DarmorGamz/Ultrasonic-Flow-Reader/docs/Flowcharts/BlockDiagram.pdf

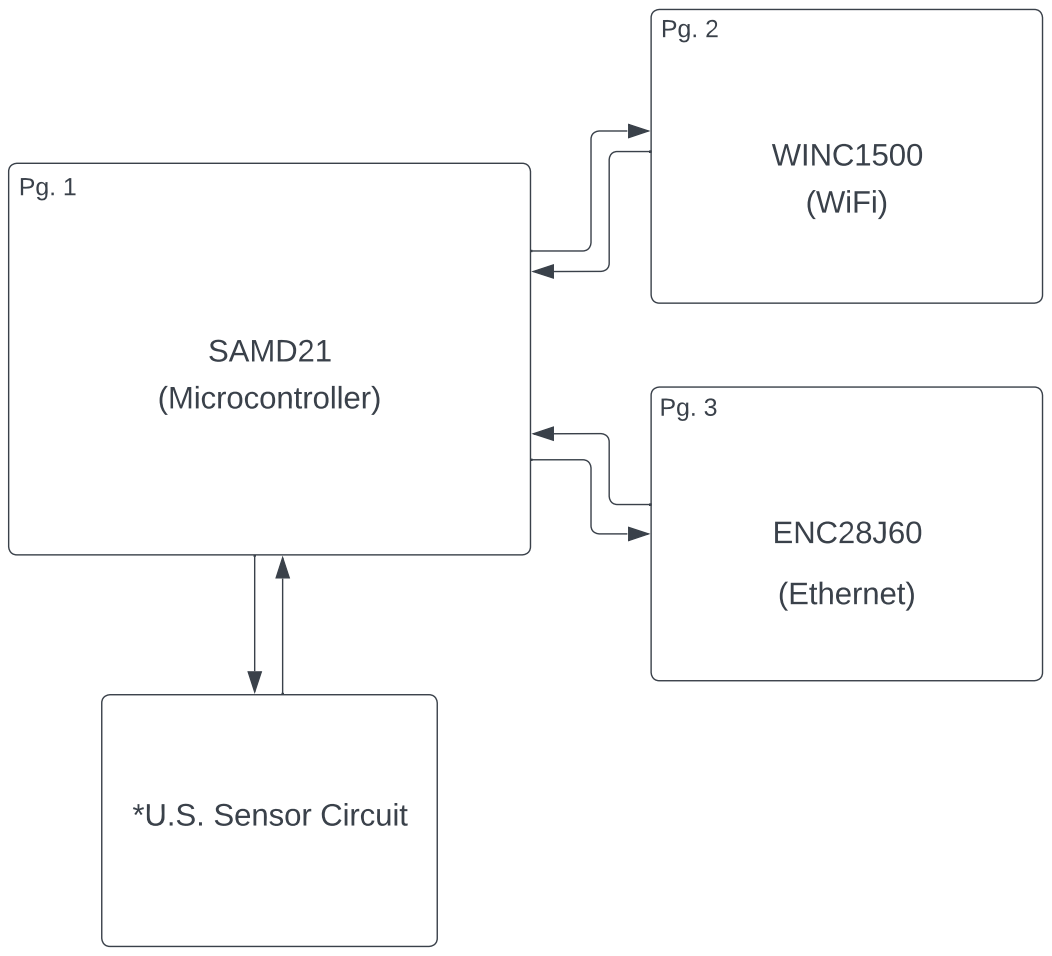
[picture p48: page 1]
SAMD21; WINC1500; ENC28J60; *U.S. Sensor Circuit; (WiFi); (Ethernet); (Microcontroller); DCA

TITLE: Ultrasonic Meter-Reader Block Diagram
REV: v1.0
DATE: 2022/11/02
