DarmorGamz/Ultrasonic-Flow-Reader/Firmware/Firmware/driver_init.h

/*
 * Code generated from Atmel Start.
 *
 * This file will be overwritten when reconfiguring your Atmel Start project.
 * Please copy examples or other code you want to keep to a separate file
 * to avoid losing it when reconfiguring.
 */
#ifndef DRIVER_INIT_INCLUDED
#define DRIVER_INIT_INCLUDED

#include "atmel_start_pins.h"

#ifdef __cplusplus
extern "C" {
#endif

#include <hal_atomic.h>
#include <hal_delay.h>
#include <hal_gpio.h>
#include <hal_init.h>
#include <hal_io.h>
#include <hal_sleep.h>

#include <hal_ext_irq.h>

#include <hal_flash.h>

#include <hal_spi_m_sync.h>
#include <hal_spi_m_sync.h>

#include <hal_delay.h>
#include <hal_timer.h>
#include <hpl_tc_base.h>
#include <hal_timer.h>
#include <hpl_tc_base.h>
#include <hal_timer.h>
#include <hpl_tc_base.h>

#include <hal_wdt.h>

extern struct flash_descriptor      FLASH_0;
extern struct spi_m_sync_descriptor WIRELESS_SPI;
extern struct spi_m_sync_descriptor ETHERNET_SPI;

extern struct timer_descriptor TIMER_0;
extern struct timer_descriptor SAMPLE_TIMER;
extern struct timer_descriptor TICK_TIMER;

extern struct wdt_descriptor WDT_0;

void FLASH_0_init(void);
void FLASH_0_CLOCK_init(void);

void WIRELESS_SPI_PORT_init(void);
void WIRELESS_SPI_CLOCK_init(void);
void WIRELESS_SPI_init(void);

void ETHERNET_SPI_PORT_init(void);
void ETHERNET_SPI_CLOCK_init(void);
void ETHERNET_SPI_init(void);

void delay_driver_init(void);

void WDT_0_CLOCK_init(void);
void WDT_0_init(void);

/**
 * \brief Perform system initialization, initialize pins and clocks for
 * peripherals
 */
void system_init(void);

#ifdef __cplusplus
}
#endif
#endif // DRIVER_INIT_INCLUDED
