DarmorGamz/Ultrasonic-Flow-Reader/Firmware/Firmware/hri/hri_port_d20.h

/**
 * \file
 *
 * \brief SAM PORT
 *
 * Copyright (c) 2017-2018 Microchip Technology Inc. and its subsidiaries.
 *
 * \asf_license_start
 *
 * \page License
 *
 * Subject to your compliance with these terms, you may use Microchip
 * software and any derivatives exclusively with Microchip products.
 * It is your responsibility to comply with third party license terms applicable
 * to your use of third party software (including open source software) that
 * may accompany Microchip software.
 *
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
 * \asf_license_stop
 *
 */

#ifdef _SAMD20_PORT_COMPONENT_
#ifndef _HRI_PORT_D20_H_INCLUDED_
#define _HRI_PORT_D20_H_INCLUDED_

#ifdef __cplusplus
extern "C" {
#endif

#include <stdbool.h>
#include <hal_atomic.h>

#if defined(ENABLE_PORT_CRITICAL_SECTIONS)
#define PORT_CRITICAL_SECTION_ENTER() CRITICAL_SECTION_ENTER()
#define PORT_CRITICAL_SECTION_LEAVE() CRITICAL_SECTION_LEAVE()
#else
#define PORT_CRITICAL_SECTION_ENTER()
#define PORT_CRITICAL_SECTION_LEAVE()
#endif

typedef uint32_t hri_port_ctrl_reg_t;
typedef uint32_t hri_port_dir_reg_t;
typedef uint32_t hri_port_in_reg_t;
typedef uint32_t hri_port_out_reg_t;
typedef uint32_t hri_port_wrconfig_reg_t;
typedef uint32_t hri_portgroup_ctrl_reg_t;
typedef uint32_t hri_portgroup_dir_reg_t;
typedef uint32_t hri_portgroup_in_reg_t;
typedef uint32_t hri_portgroup_out_reg_t;
typedef uint32_t hri_portgroup_wrconfig_reg_t;
typedef uint8_t  hri_port_pincfg_reg_t;
typedef uint8_t  hri_port_pmux_reg_t;
typedef uint8_t  hri_portgroup_pincfg_reg_t;
typedef uint8_t  hri_portgroup_pmux_reg_t;

static inline void hri_portgroup_set_DIR_DIR_bf(const void *const hw, hri_port_dir_reg_t mask)
{
	((PortGroup *)hw)->DIRSET.reg = PORT_DIR_DIR(mask);
}

static inline hri_port_dir_reg_t hri_portgroup_get_DIR_DIR_bf(const void *const hw, hri_port_dir_reg_t mask)
{
	uint32_t tmp;
	tmp = ((PortGroup *)hw)->DIR.reg;
	tmp = (tmp & PORT_DIR_DIR(mask)) >> PORT_DIR_DIR_Pos;
	return tmp;
}

static inline hri_port_dir_reg_t hri_portgroup_read_DIR_DIR_bf(const void *const hw)
{
	uint32_t tmp;
	tmp = ((PortGroup *)hw)->DIR.reg;
	tmp = (tmp & PORT_DIR_DIR_Msk) >> PORT_DIR_DIR_Pos;
	return tmp;
}

static inline void hri_portgroup_write_DIR_DIR_bf(const void *const hw, hri_port_dir_reg_t data)
{
	((PortGroup *)hw)->DIRSET.reg = PORT_DIR_DIR(data);
	((PortGroup *)hw)->DIRCLR.reg = ~PORT_DIR_DIR(data);
}

static inline void hri_portgroup_clear_DIR_DIR_bf(const void *const hw, hri_port_dir_reg_t mask)
{
	((PortGroup *)hw)->DIRCLR.reg = PORT_DIR_DIR(mask);
}

static inline void hri_portgroup_toggle_DIR_DIR_bf(const void *const hw, hri_port_dir_reg_t mask)
{
	((PortGroup *)hw)->DIRTGL.reg = PORT_DIR_DIR(mask);
}

static inline void hri_portgroup_set_DIR_reg(const void *const hw, hri_port_dir_reg_t mask)
{
	((PortGroup *)hw)->DIRSET.reg = mask;
}

static inline hri_port_dir_reg_t hri_portgroup_get_DIR_reg(const void *const hw, hri_port_dir_reg_t mask)
{
	uint32_t tmp;
	tmp = ((PortGroup *)hw)->DIR.reg;
	tmp &= mask;
	return tmp;
}

static inline hri_port_dir_reg_t hri_portgroup_read_DIR_reg(const void *const hw)
{
	return ((PortGroup *)hw)->DIR.reg;
}

static inline void hri_portgroup_write_DIR_reg(const void *const hw, hri_port_dir_reg_t data)
{
	((PortGroup *)hw)->DIRSET.reg = data;
	((PortGroup *)hw)->DIRCLR.reg = ~data;
}

static inline void hri_portgroup_clear_DIR_reg(const void *const hw, hri_port_dir_reg_t mask)
{
	((PortGroup *)hw)->DIRCLR.reg = mask;
}

static inline void hri_portgroup_toggle_DIR_reg(const void *const hw, hri_port_dir_reg_t mask)
{
	((PortGroup *)hw)->DIRTGL.reg = mask;
}

static inline void hri_portgroup_set_OUT_OUT_bf(const void *const hw, hri_port_out_reg_t mask)
{
	((PortGroup *)hw)->OUTSET.reg = PORT_OUT_OUT(mask);
}

static inline hri_port_out_reg_t hri_portgroup_get_OUT_OUT_bf(const void *const hw, hri_port_out_reg_t mask)
{
	uint32_t tmp;
	tmp = ((PortGroup *)hw)->OUT.reg;
	tmp = (tmp & PORT_OUT_OUT(mask)) >> PORT_OUT_OUT_Pos;
	return tmp;
}

static inline hri_port_out_reg_t hri_portgroup_read_OUT_OUT_bf(const void *const hw)
{
	uint32_t tmp;
	tmp = ((PortGroup *)hw)->OUT.reg;
	tmp = (tmp & PORT_OUT_OUT_Msk) >> PORT_OUT_OUT_Pos;
	return tmp;
}

static inline void hri_portgroup_write_OUT_OUT_bf(const void *const hw, hri_port_out_reg_t data)
{
	((PortGroup *)hw)->OUTSET.reg = PORT_OUT_OUT(data);
	((PortGroup *)hw)->OUTCLR.reg = ~PORT_OUT_OUT(data);
}

static inline void hri_portgroup_clear_OUT_OUT_bf(const void *const hw, hri_port_out_reg_t mask)
{
	((PortGroup *)hw)->OUTCLR.reg = PORT_OUT_OUT(mask);
}

static inline void hri_portgroup_toggle_OUT_OUT_bf(const void *const hw, hri_port_out_reg_t mask)
{
	((PortGroup *)hw)->OUTTGL.reg = PORT_OUT_OUT(mask);
}

static inline void hri_portgroup_set_OUT_reg(const void *const hw, hri_port_out_reg_t mask)
{
	((PortGroup *)hw)->OUTSET.reg = mask;
}

static inline hri_port_out_reg_t hri_portgroup_get_OUT_reg(const void *const hw, hri_port_out_reg_t mask)
{
	uint32_t tmp;
	tmp = ((PortGroup *)hw)->OUT.reg;
	tmp &= mask;
	return tmp;
}

static inline hri_port_out_reg_t hri_portgroup_read_OUT_reg(const void *const hw)
{
	return ((PortGroup *)hw)->OUT.reg;
}

static inline void hri_portgroup_write_OUT_reg(const void *const hw, hri_port_out_reg_t data)
{
	((PortGroup *)hw)->OUTSET.reg = data;
	((PortGroup *)hw)->OUTCLR.reg = ~data;
}

static inline void hri_portgroup_clear_OUT_reg(const void *const hw, hri_port_out_reg_t mask)
{
	((PortGroup *)hw)->OUTCLR.reg = mask;
}

static inline void hri_portgroup_toggle_OUT_reg(const void *const hw, hri_port_out_reg_t mask)
{
	((PortGroup *)hw)->OUTTGL.reg = mask;
}

static inline hri_port_in_reg_t hri_portgroup_get_IN_IN_bf(const void *const hw, hri_port_in_reg_t mask)
{
	return (((PortGroup *)hw)->IN.reg & PORT_IN_IN(mask)) >> PORT_IN_IN_Pos;
}

static inline hri_port_in_reg_t hri_portgroup_read_IN_IN_bf(const void *const hw)
{
	return (((PortGroup *)hw)->IN.reg & PORT_IN_IN_Msk) >> PORT_IN_IN_Pos;
}

static inline hri_port_in_reg_t hri_portgroup_get_IN_reg(const void *const hw, hri_port_in_reg_t mask)
{
	uint32_t tmp;
	tmp = ((PortGroup *)hw)->IN.reg;
	tmp &= mask;
	return tmp;
}

static inline hri_port_in_reg_t hri_portgroup_read_IN_reg(const void *const hw)
{
	return ((PortGroup *)hw)->IN.reg;
}

static inline void hri_portgroup_set_CTRL_SAMPLING_bf(const void *const hw, hri_port_ctrl_reg_t mask)
{
	PORT_CRITICAL_SECTION_ENTER();
	((PortGroup *)hw)->CTRL.reg |= PORT_CTRL_SAMPLING(mask);
	PORT_CRITICAL_SECTION_LEAVE();
}

static inline hri_port_ctrl_reg_t hri_portgroup_get_CTRL_SAMPLING_bf(const void *const hw, hri_port_ctrl_reg_t mask)
{
	uint32_t tmp;
	tmp = ((PortGroup *)hw)->CTRL.reg;
	tmp = (tmp & PORT_CTRL_SAMPLING(mask)) >> PORT_CTRL_SAMPLING_Pos;
	return tmp;
}

static inline void hri_portgroup_write_CTRL_SAMPLING_bf(const void *const hw, hri_port_ctrl_reg_t data)
{
	uint32_t tmp;
	PORT_CRITICAL_SECTION_ENTER();
	tmp = ((PortGroup *)hw)->CTRL.reg;
	tmp &= ~PORT_CTRL_SAMPLING_Msk;
	tmp |= PORT_CTRL_SAMPLING(data);
	((PortGroup *)hw)->CTRL.reg = tmp;
	PORT_CRITICAL_SECTION_LEAVE();
}

static inline void hri_portgroup_clear_CTRL_SAMPLING_bf(const void *const hw, hri_port_ctrl_reg_t mask)
{
	PORT_CRITICAL_SECTION_ENTER();
	((PortGroup *)hw)->CTRL.reg &= ~PORT_CTRL_SAMPLING(mask);
	PORT_CRITICAL_SECTION_LEAVE();
}

static inline void hri_portgroup_toggle_CTRL_SAMPLING_bf(const void *const hw, hri_port_ctrl_reg_t mask)
{
	PORT_CRITICAL_SECTION_ENTER();
	((PortGroup *)hw)->CTRL.reg ^= PORT_CTRL_SAMPLING(mask);
	PORT_CRITICAL_SECTION_LEAVE();
}

static inline hri_port_ctrl_reg_t hri_portgroup_read_CTRL_SAMPLING_bf(const void *const hw)
{
	uint32_t tmp;
	tmp = ((PortGroup *)hw)->CTRL.reg;
	tmp = (tmp & PORT_CTRL_SAMPLING_Msk) >> PORT_CTRL_SAMPLING_Pos;
	return tmp;
}
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
